LaskaKit/MAX31865_PT100x/img/3.jpg

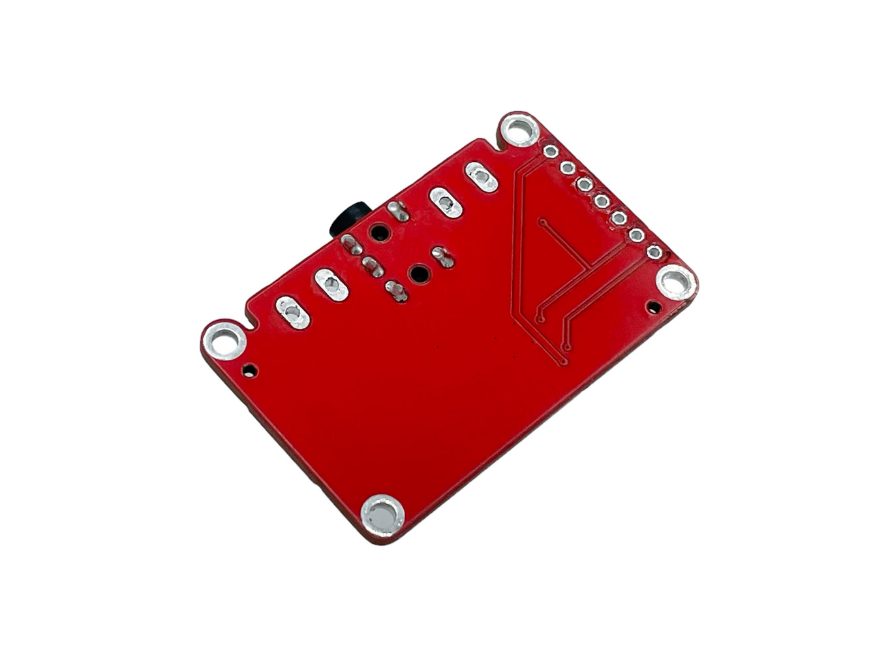
img/3.jpg
