LaskaKit/MAX31865_PT100x/img/4.jpg

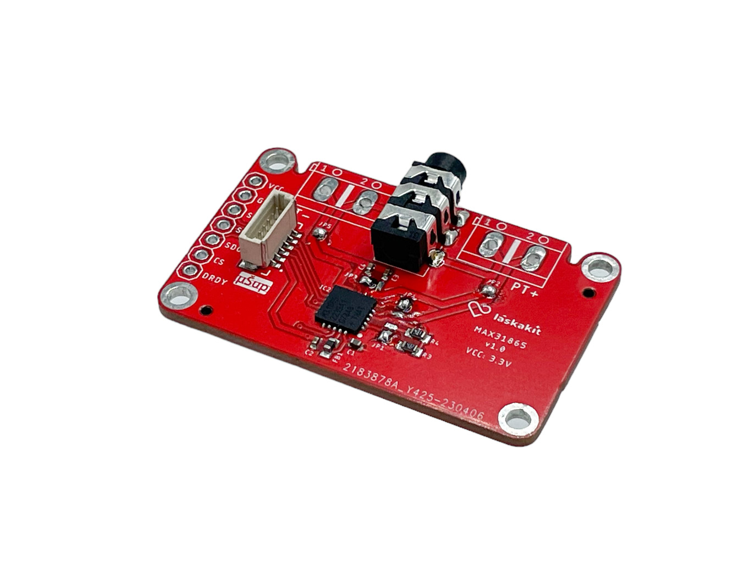
img/4.jpg
